FutureProofHomes/Satellite1-Enclosures/DIY Enclosures/In Ceiling Enclosures/pictures/Screws.png

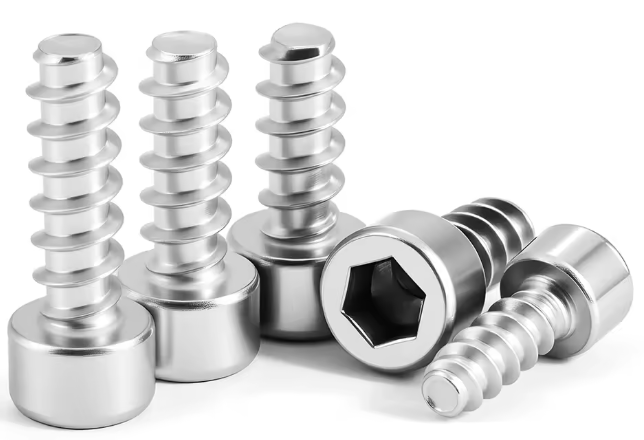
DIY Enclosures/In Ceiling Enclosures/pictures/Screws.png
