FutureProofHomes/Satellite1-Enclosures/OEM Enclosures/Satellite1 Smart Speaker Enclosure Kit/Geometry Files/STEP/Bonus/Minimalistic Chamber (optional 3525 speaker).step

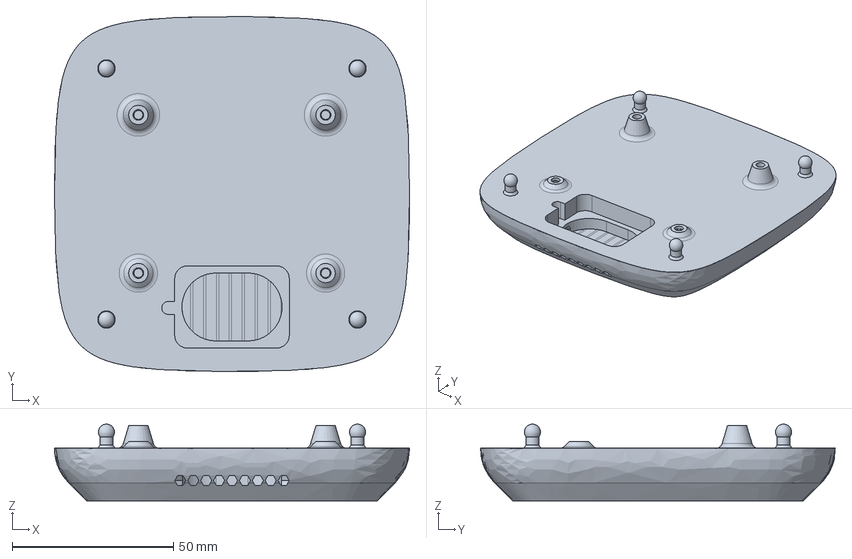
[picture p22: CAD file, 2026-02-08]
OEM Enclosures/Satellite1 Smart Speaker Enclosure Kit/Geometry Files/STEP/Bonus/Minimalistic Chamber (optional 3525 speaker).step
110.0 x 110.0 x 23.8 mm
