FutureProofHomes/Satellite1-Enclosures/OEM Enclosures/Satellite1 Smart Speaker Enclosure Kit/Geometry Files/STEP/LED Diffuser.step

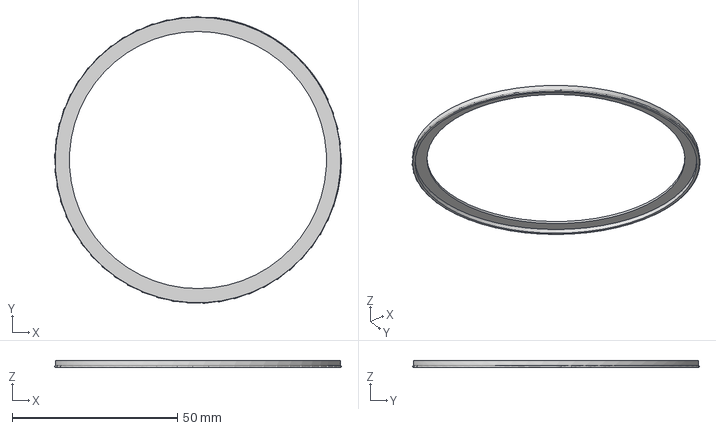
[picture p23: CAD file, 2025-12-31]
OEM Enclosures/Satellite1 Smart Speaker Enclosure Kit/Geometry Files/STEP/LED Diffuser.step
86.8 x 86.8 x 2.00 mm
