FutureProofHomes/Satellite1-Enclosures/OEM Enclosures/Satellite1 Smart Speaker Enclosure Kit/Geometry Files/STEP/MultiMaterial/Top Plate (MultiMaterial including diffuser).step

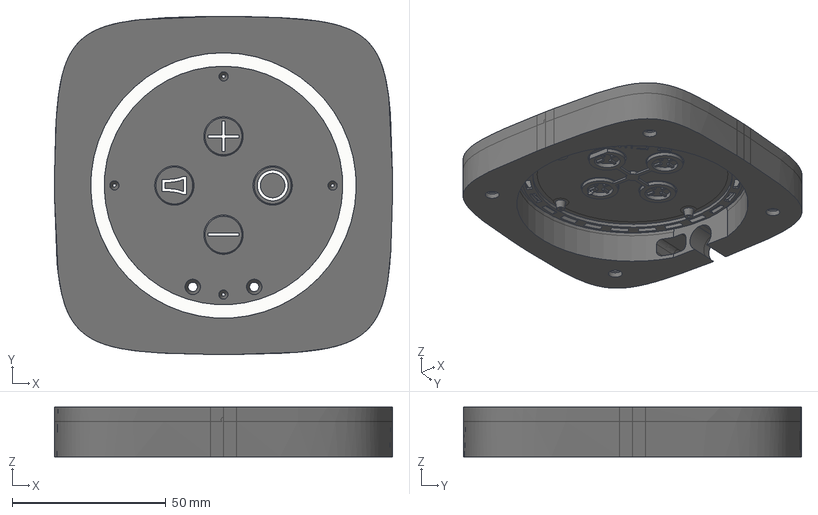
[picture p24: CAD file, 2025-12-31]
OEM Enclosures/Satellite1 Smart Speaker Enclosure Kit/Geometry Files/STEP/MultiMaterial/Top Plate (MultiMaterial including diffuser).step
110.0 x 110.0 x 16.2 mm
Top multimaterial
Speaker symbol led pipe (2)
Speaker symbol (1)
Minus symbol (1)
Ring symbol (1)
Plus symbol (1)
LED Ring diffuser
