FutureProofHomes/Satellite1-Enclosures/OEM Enclosures/Satellite1.1 Smart Speaker Enclosure Kit/Geometry Files/STL/Sat1.x large - Chamber back - Wifi pocket + Bass port.stl

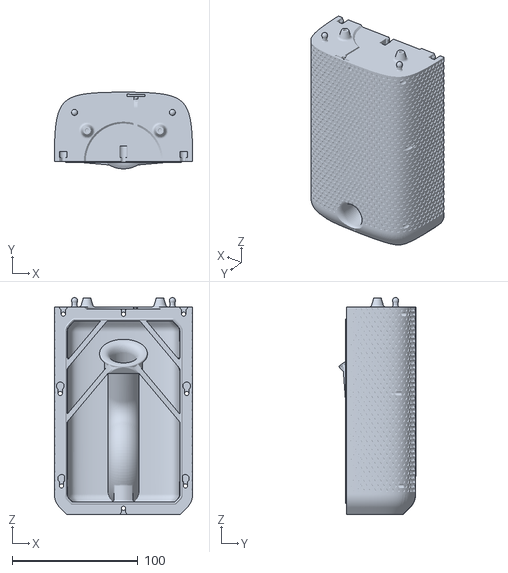
[picture p25: CAD file, 2026-07-22]
OEM Enclosures/Satellite1.1 Smart Speaker Enclosure Kit/Geometry Files/STL/Sat1.x large - Chamber back - Wifi pocket + Bass port.stl
110.0 x 61.0 x 172.5
