FutureProofHomes/Satellite1-Enclosures/OEM Enclosures/Satellite1.1 Smart Speaker Enclosure Kit/Sat 1.x Enclosure - singlematerial (Orca Slicer Projectfile).3mf

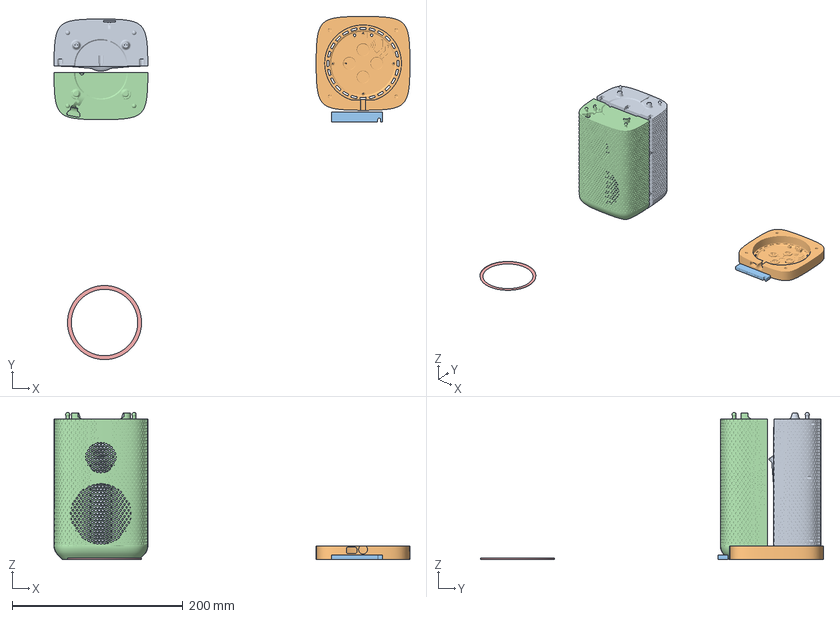
[picture p26: CAD file, 2026-04-05]
OEM Enclosures/Satellite1.1 Smart Speaker Enclosure Kit/Sat 1.x Enclosure - singlematerial (Orca Slicer Projectfile).3mf
417.2 x 402.1 x 172.5 mm
Sat1.x - Chamber back - Wifi pocket + Bass port.stl
Sat1.x - Top Plate single material.stl
Sat1.x - Screwing guide.stl
Sat1.x - Chamber front - FPH Woofer +Tweeter + LD2450 pocket.stl
Sat1.x - Top Plate single material - LED Diffuser.stl
