FutureProofHomes/Satellite1-Enclosures/DIY Enclosures/Cylindrical Enclosures/Bambu Studio - Sat1 Dev Kit Speaker Enclosure.3mf

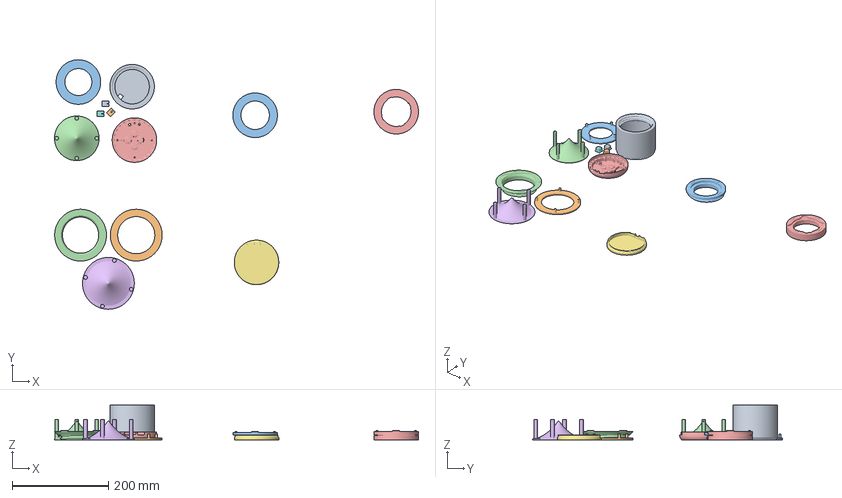
[picture p27: CAD file, 2025-05-12]
DIY Enclosures/Cylindrical Enclosures/Bambu Studio - Sat1 Dev Kit Speaker Enclosure.3mf
755.2 x 517.7 x 72.1 mm
Speaker Chamber Threaded.stl
Stand Lock Ring - GRS-3FR-4.stl
Speaker Adapter - RS75-4.stl
Speaker Adapter - GRS-3FR-4.stl
Speaker Adapter - TEBM46C-20N.stl
Speaker Stand - GRS 3FR-4.stl
(Optional) Dev Kit UFO Base for No Speaker.stl
1.5mm Wire Cover.stl
1mm Wire Cover.stl
2mm Wire Cover.stl
Lock Ring.stl
Speaker Stand.stl
Dev Kit UFO Enclosure.stl
