FutureProofHomes/Satellite1-Enclosures/DIY Enclosures/Cylindrical Enclosures/Geometry Files/STEP/General Parts/Speaker Chamber Threaded.step

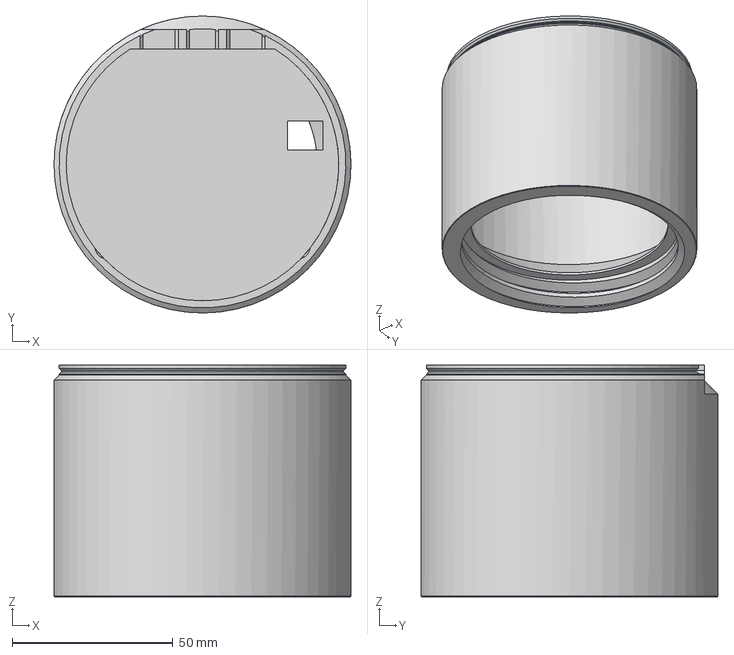
[picture p28: CAD file, 2025-05-12]
DIY Enclosures/Cylindrical Enclosures/Geometry Files/STEP/General Parts/Speaker Chamber Threaded.step
92.4 x 92.4 x 72.1 mm
