FutureProofHomes/Satellite1-Enclosures/DIY Enclosures/Squircle Enclosures/Geometry Files/STEP/Mid-Plate/Mid-Plate.step

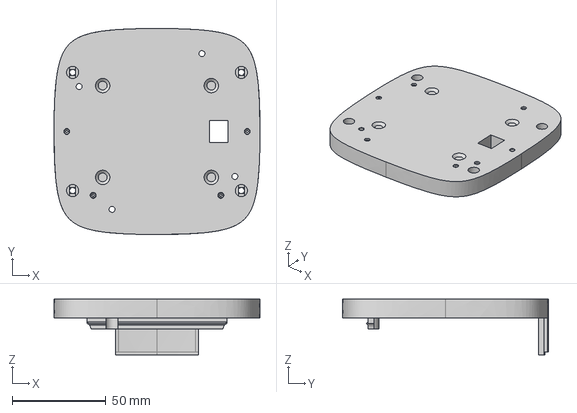
[picture p29: CAD file, 2025-06-02]
DIY Enclosures/Squircle Enclosures/Geometry Files/STEP/Mid-Plate/Mid-Plate.step
110.0 x 110.0 x 29.7 mm
