FutureProofHomes/Satellite1-Enclosures/DIY Enclosures/Squircle Enclosures/Geometry Files/STEP/Speaker Chamber/3-Watt Speaker Chamber.step

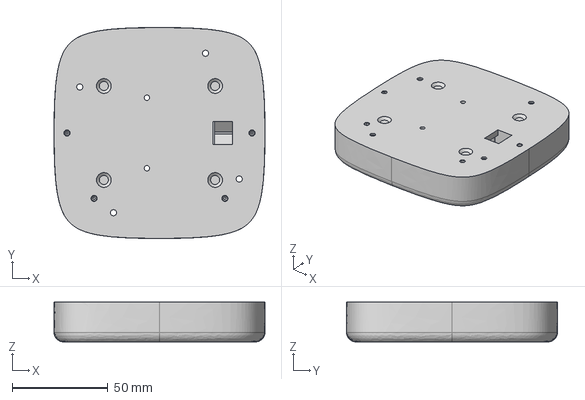
[picture p30: CAD file, 2025-06-04]
DIY Enclosures/Squircle Enclosures/Geometry Files/STEP/Speaker Chamber/3-Watt Speaker Chamber.step
110.0 x 110.0 x 20.7 mm
