FutureProofHomes/Satellite1-Enclosures/DIY Enclosures/Squircle Enclosures/Geometry Files/STEP/Squircle Top/Top Plate Snap-In Diffuser Ring.step

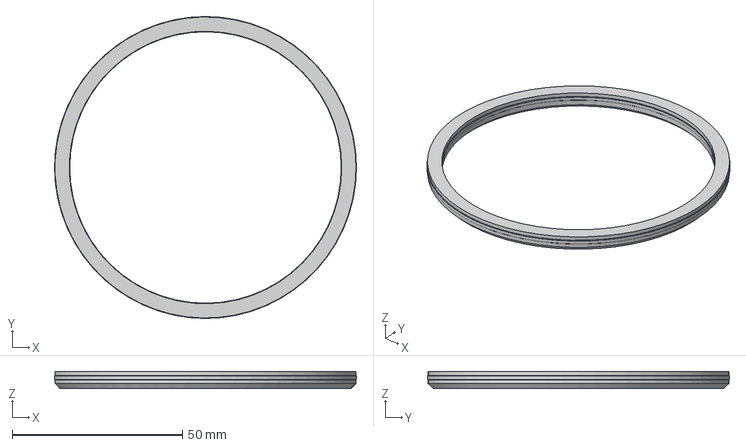
[picture p31: CAD file, 2025-06-11]
DIY Enclosures/Squircle Enclosures/Geometry Files/STEP/Squircle Top/Top Plate Snap-In Diffuser Ring.step
88.8 x 88.8 x 5.00 mm
