FutureProofHomes/Satellite1-Enclosures/DIY Enclosures/Squircle Enclosures/Geometry Files/STEP/Wire Covers/Wire Cover 1.5mm.step

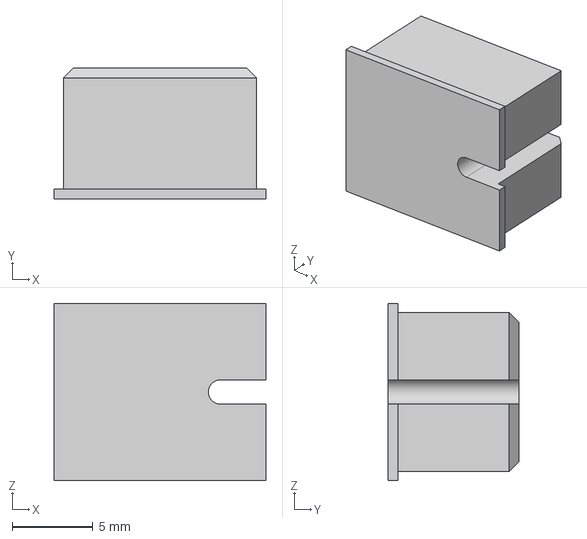
[picture p32: CAD file, 2025-06-03]
DIY Enclosures/Squircle Enclosures/Geometry Files/STEP/Wire Covers/Wire Cover 1.5mm.step
13.2 x 8.10 x 11.0 mm
