FutureProofHomes/Satellite1-Enclosures/OEM Enclosures/Satellite1 Smart Speaker Enclosure Kit/Geometry Files/STEP/Top Plate.step

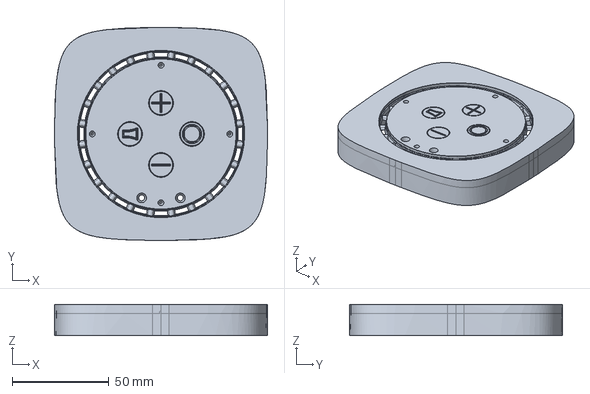
[picture p33: CAD file, 2025-12-31]
OEM Enclosures/Satellite1 Smart Speaker Enclosure Kit/Geometry Files/STEP/Top Plate.step
110.0 x 110.0 x 16.2 mm
