FutureProofHomes/Satellite1-Enclosures/OEM Enclosures/Satellite1.1 Smart Speaker Enclosure Kit/Geometry Files/STL/Sat1.x - Top Plate multi material.3mf

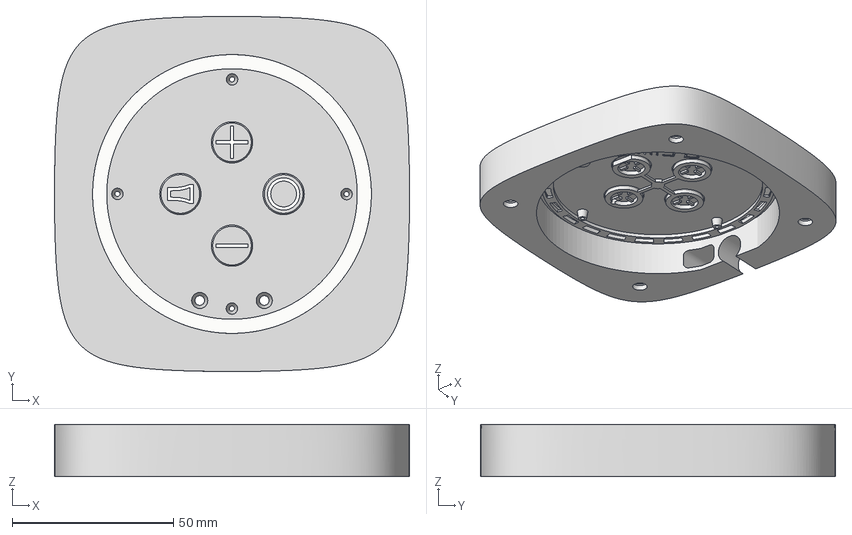
[picture p34: CAD file, 2026-04-05]
OEM Enclosures/Satellite1.1 Smart Speaker Enclosure Kit/Geometry Files/STL/Sat1.x - Top Plate multi material.3mf
110.0 x 110.0 x 16.1 mm
Diffuser
Minus symbol
Plus symbol
Ring symbol
Speaker symbol
Top multimaterial
