FutureProofHomes/Satellite1-Enclosures/OEM Enclosures/Satellite1.1 Smart Speaker Enclosure Kit/Sat 1.x Enclosure - multimaterial white (Bambu Studio Projectfile).3mf

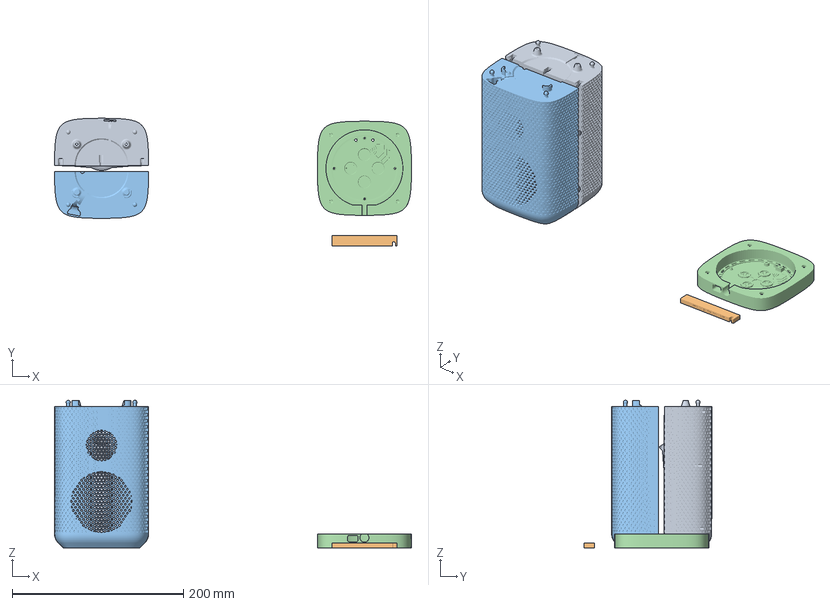
[picture p35: CAD file, 2026-04-05]
OEM Enclosures/Satellite1.1 Smart Speaker Enclosure Kit/Sat 1.x Enclosure - multimaterial white (Bambu Studio Projectfile).3mf
417.2 x 149.0 x 172.5 mm
Chamber back - Wifi pocket + Bass port.stl
Screw guide
Chamber front - FPH Woofer +Tweeter + LD2450 pocket.stl
Top - Multimaterial
