FutureProofHomes/Satellite1-Enclosures/DIY Enclosures/Cylindrical Enclosures/Geometry Files/STEP/Speaker - GRS 3FR-4/Speaker Stand - GRS 3FR-4.step

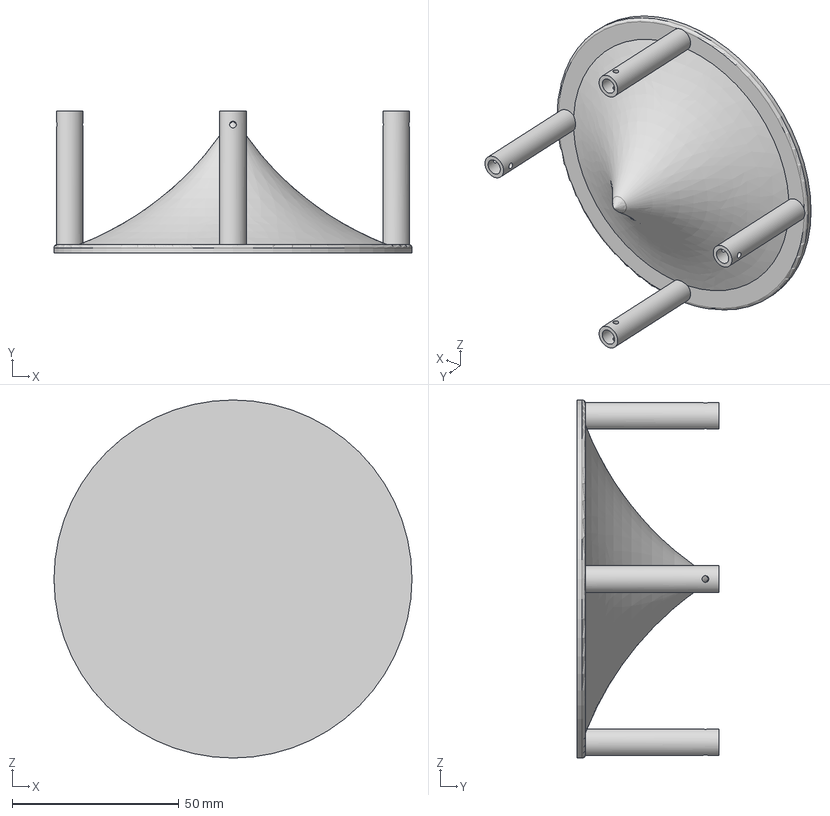
[picture p37: CAD file, 2025-05-03]
DIY Enclosures/Cylindrical Enclosures/Geometry Files/STEP/Speaker - GRS 3FR-4/Speaker Stand - GRS 3FR-4.step
107.5 x 42.5 x 107.5 mm
