FutureProofHomes/Satellite1-Enclosures/DIY Enclosures/Squircle Enclosures/Geometry Files/STEP/Speaker Chamber/3-Watt Speaker Chamber Legs x 4.step

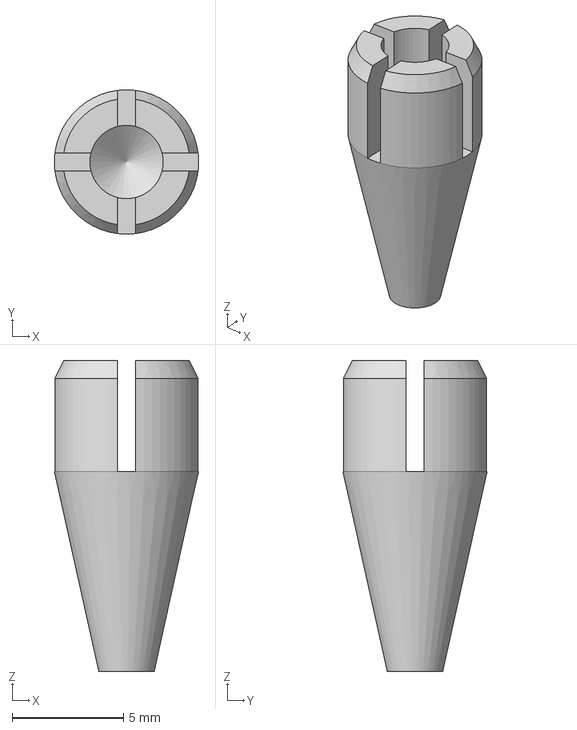
[picture p38: CAD file, 2025-06-04]
DIY Enclosures/Squircle Enclosures/Geometry Files/STEP/Speaker Chamber/3-Watt Speaker Chamber Legs x 4.step
6.50 x 6.49 x 14.0 mm
