FutureProofHomes/Satellite1-Enclosures/DIY Enclosures/Squircle Enclosures/Geometry Files/STEP/Speaker Plates/25-Watt Speaker Plate Tectonic TEBM46C20N-4 v5.step

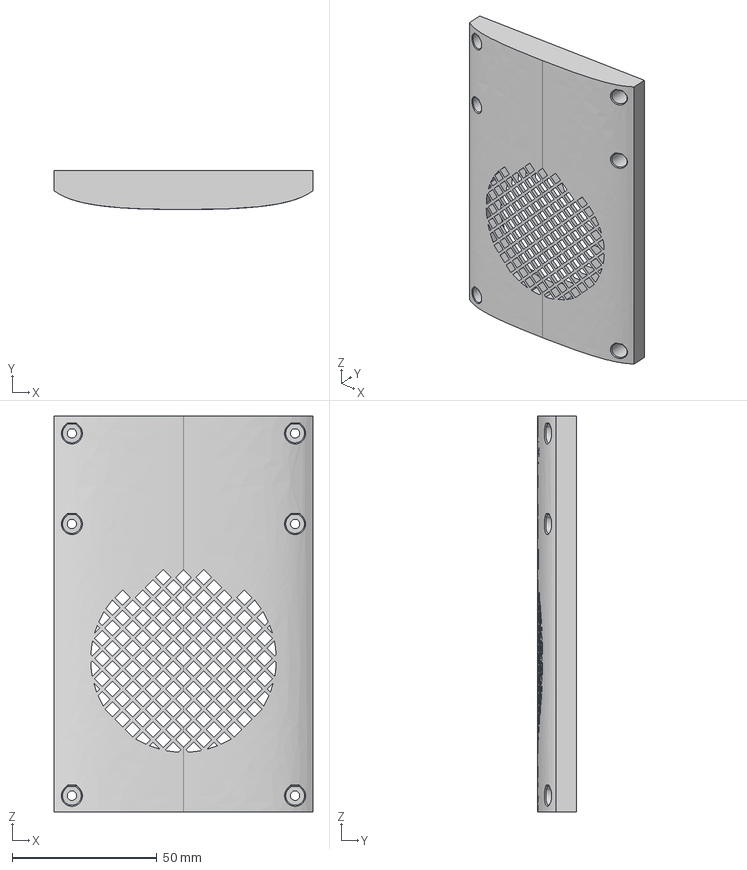
[picture p39: CAD file, 2025-05-26]
DIY Enclosures/Squircle Enclosures/Geometry Files/STEP/Speaker Plates/25-Watt Speaker Plate Tectonic TEBM46C20N-4 v5.step
89.2 x 13.5 x 136.6 mm
