FutureProofHomes/Satellite1-Enclosures/DIY Enclosures/Squircle Enclosures/Geometry Files/STEP/Squircle Top/Top Plate.step

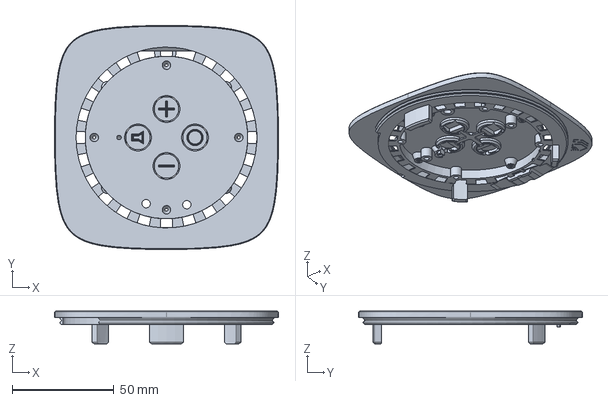
[picture p40: CAD file, 2025-06-11]
DIY Enclosures/Squircle Enclosures/Geometry Files/STEP/Squircle Top/Top Plate.step
110.0 x 110.0 x 16.0 mm
