FutureProofHomes/Satellite1-Enclosures/OEM Enclosures/Satellite1.1 Smart Speaker Enclosure Kit/Sat 1.x Enclosure - singlematerial (Bambu Studio Projectfile).3mf

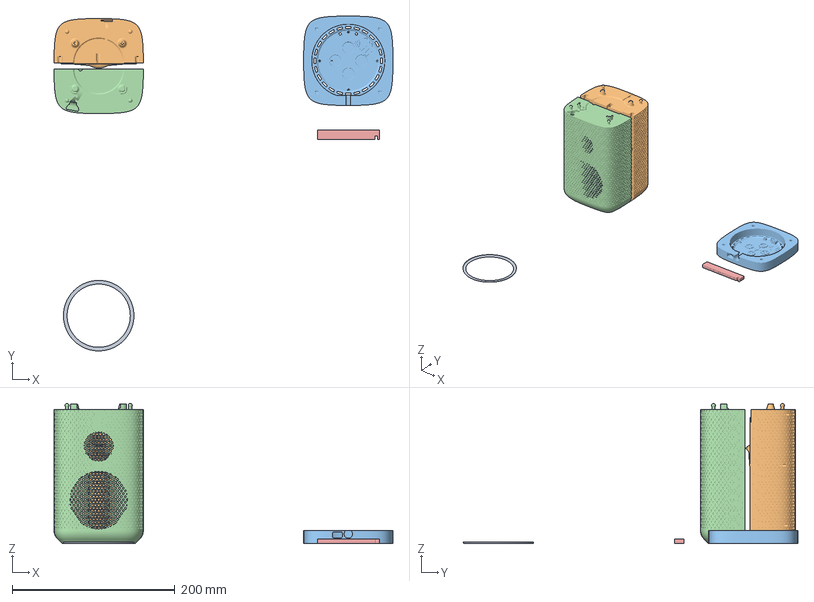
[picture p42: CAD file, 2026-04-05]
OEM Enclosures/Satellite1.1 Smart Speaker Enclosure Kit/Sat 1.x Enclosure - singlematerial (Bambu Studio Projectfile).3mf
417.2 x 412.1 x 172.5 mm
Top - LED diffuser.stl
Chamber back - Wifi pocket + Bass port.stl
Top.stl
Chamber front - FPH Woofer +Tweeter + LD2450 pocket.stl
Screw guide
