FutureProofHomes/Satellite1-Enclosures/DIY Enclosures/Cylindrical Enclosures/Geometry Files/STEP/General Parts/(Optional) Dev Kit UFO Base for No Speaker.step

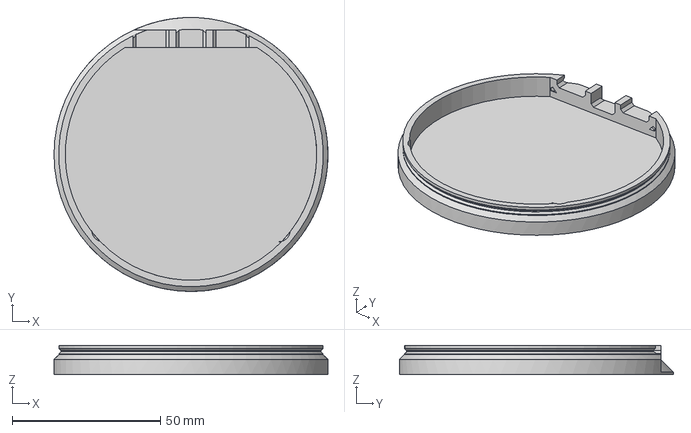
[picture p43: CAD file, 2025-05-06]
DIY Enclosures/Cylindrical Enclosures/Geometry Files/STEP/General Parts/(Optional) Dev Kit UFO Base for No Speaker.step
92.4 x 92.4 x 9.80 mm
