FutureProofHomes/Satellite1-Enclosures/DIY Enclosures/Squircle Enclosures/Geometry Files/STEP/Speaker Chamber/15-Watt Speaker Chamber.step

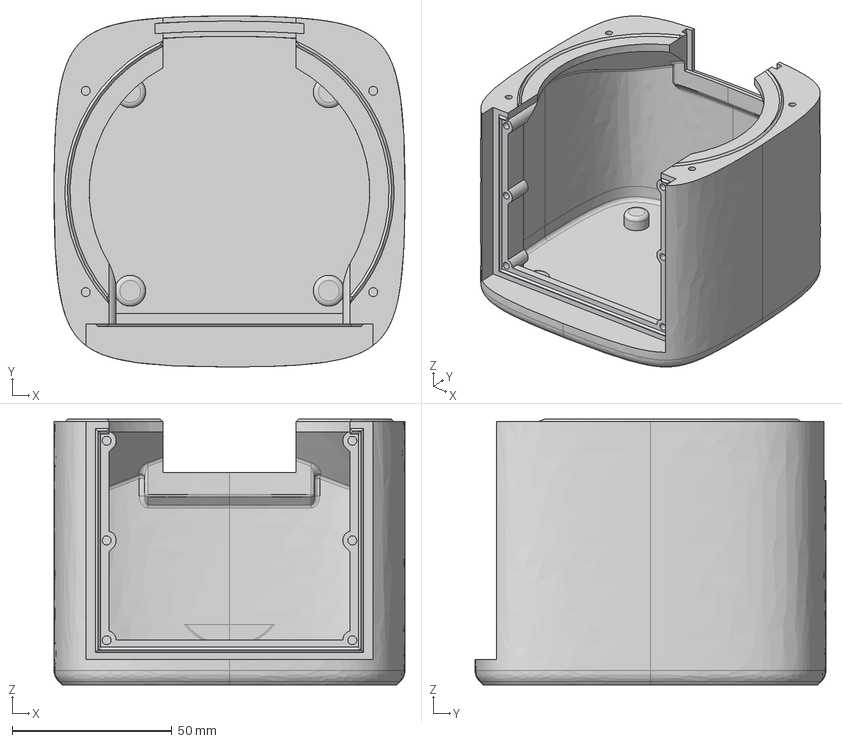
[picture p44: CAD file, 2025-06-04]
DIY Enclosures/Squircle Enclosures/Geometry Files/STEP/Speaker Chamber/15-Watt Speaker Chamber.step
110.0 x 110.0 x 83.3 mm
