FutureProofHomes/Satellite1-Enclosures/DIY Enclosures/Cylindrical Enclosures/Geometry Files/STEP/General Parts/1.5mm Wire Cover.step

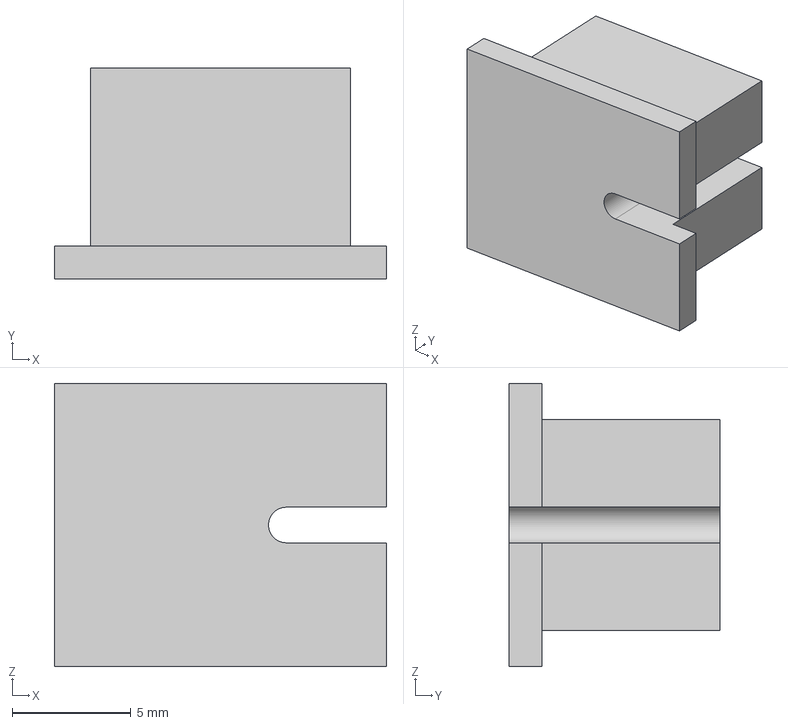
[picture p48: CAD file, 2025-05-06]
DIY Enclosures/Cylindrical Enclosures/Geometry Files/STEP/General Parts/1.5mm Wire Cover.step
14.0 x 8.90 x 11.9 mm
