FutureProofHomes/Satellite1-Enclosures/DIY Enclosures/Squircle Enclosures/Geometry Files/STEP/Speaker Chamber/25-Watt Speaker Chamber Anti-Slip Ring.step

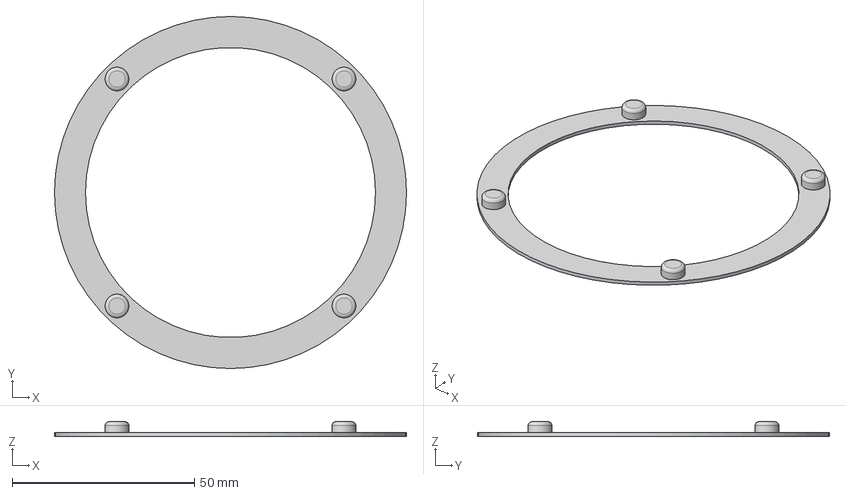
[picture p49: CAD file, 2025-05-26]
DIY Enclosures/Squircle Enclosures/Geometry Files/STEP/Speaker Chamber/25-Watt Speaker Chamber Anti-Slip Ring.step
96.5 x 96.5 x 4.00 mm
