FutureProofHomes/Satellite1-Enclosures/DIY Enclosures/Squircle Enclosures/Geometry Files/STEP/Speaker Plates/25-Watt Speaker Plate Dayton Audio PC83-4 3in.step

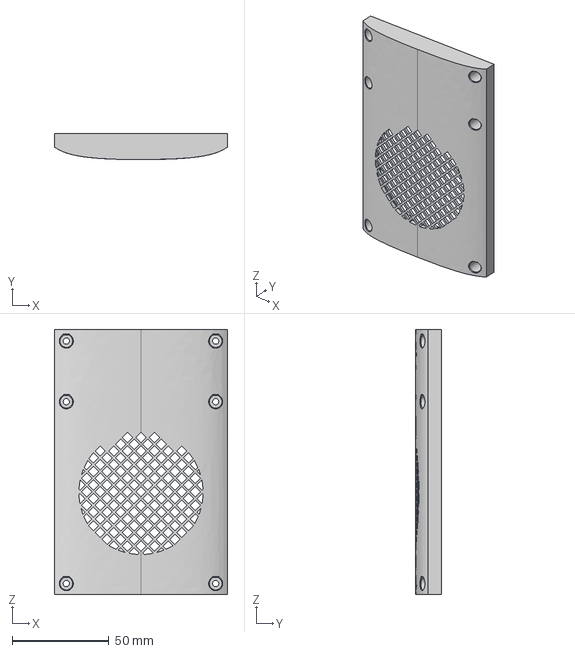
[picture p50: CAD file, 2025-05-26]
DIY Enclosures/Squircle Enclosures/Geometry Files/STEP/Speaker Plates/25-Watt Speaker Plate Dayton Audio PC83-4 3in.step
89.2 x 13.5 x 136.6 mm
