FutureProofHomes/Satellite1-Enclosures/DIY Enclosures/Squircle Enclosures/Geometry Files/STEP/Squircle Top/Top Plate MM Diffuser Ring.step

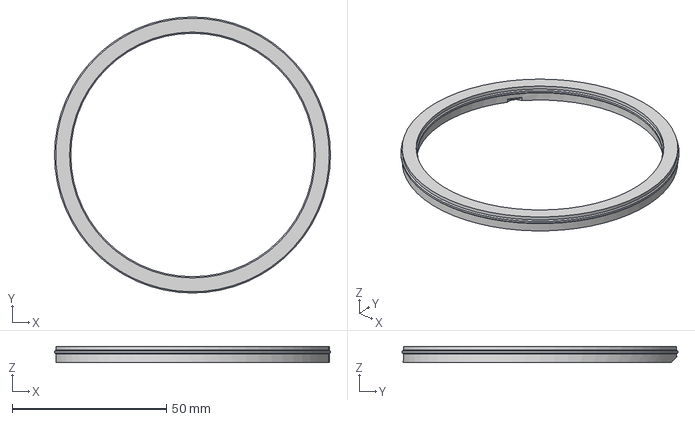
[picture p51: CAD file, 2025-06-11]
DIY Enclosures/Squircle Enclosures/Geometry Files/STEP/Squircle Top/Top Plate MM Diffuser Ring.step
89.6 x 89.6 x 5.20 mm
