FutureProofHomes/Satellite1-Enclosures/DIY Enclosures/Cylindrical Enclosures/Geometry Files/STEP/General Parts/Dev Kit UFO Enclosure.step

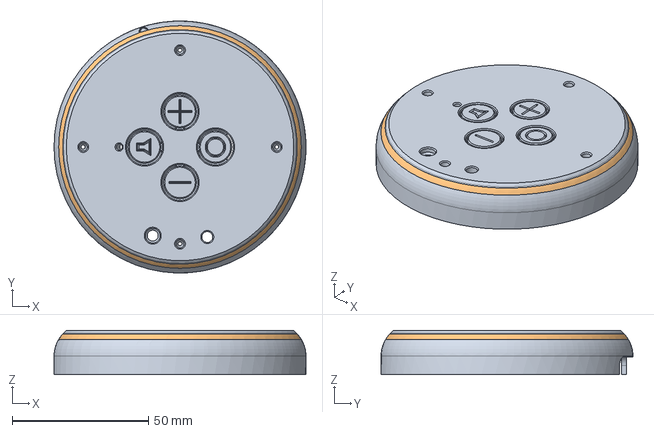
[picture p52: CAD file, 2025-05-06]
DIY Enclosures/Cylindrical Enclosures/Geometry Files/STEP/General Parts/Dev Kit UFO Enclosure.step
92.4 x 92.4 x 16.2 mm
