FutureProofHomes/Satellite1-Enclosures/DIY Enclosures/Squircle Enclosures/Geometry Files/STEP/Squircle Top/Top Plate MM Buttons.step

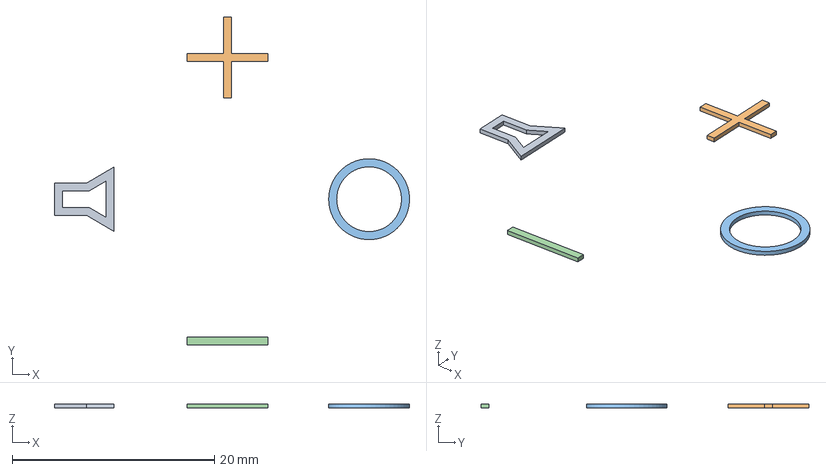
[picture p53: CAD file, 2025-06-04]
DIY Enclosures/Squircle Enclosures/Geometry Files/STEP/Squircle Top/Top Plate MM Buttons.step
35.1 x 32.4 x 0.4 mm
