FutureProofHomes/Satellite1-Enclosures/DIY Enclosures/Cylindrical Enclosures/Geometry Files/STEP/General Parts/Lock Ring.step

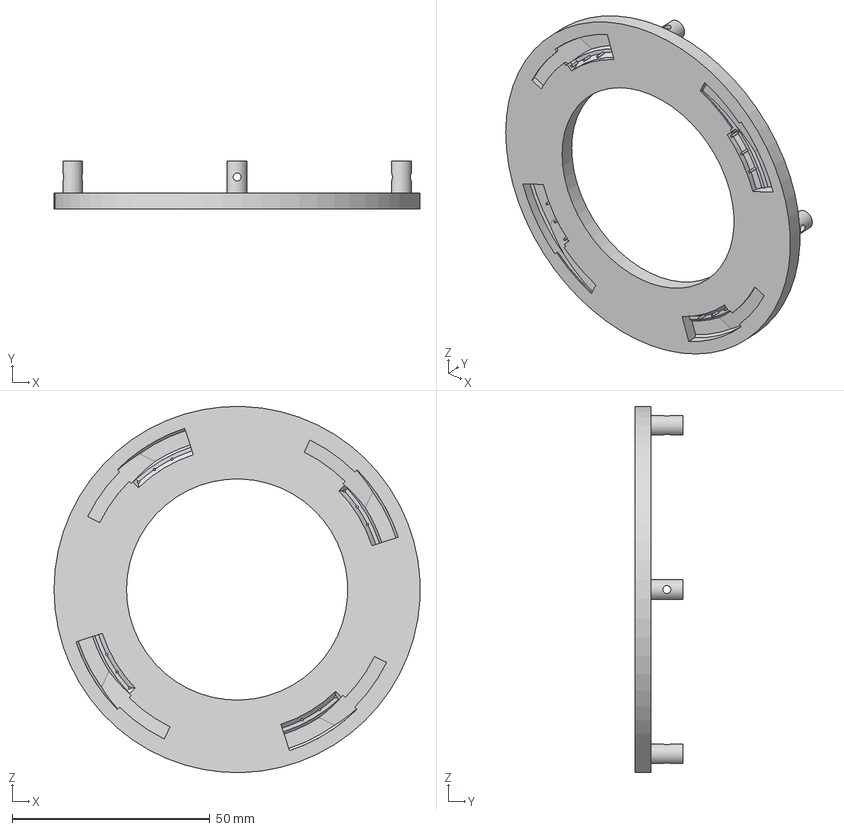
[picture p54: CAD file, 2025-05-06]
DIY Enclosures/Cylindrical Enclosures/Geometry Files/STEP/General Parts/Lock Ring.step
92.4 x 12.0 x 92.5 mm
