FutureProofHomes/Satellite1-Enclosures/DIY Enclosures/Squircle Enclosures/Geometry Files/STEP/Squircle Top/PCB Spacer.step

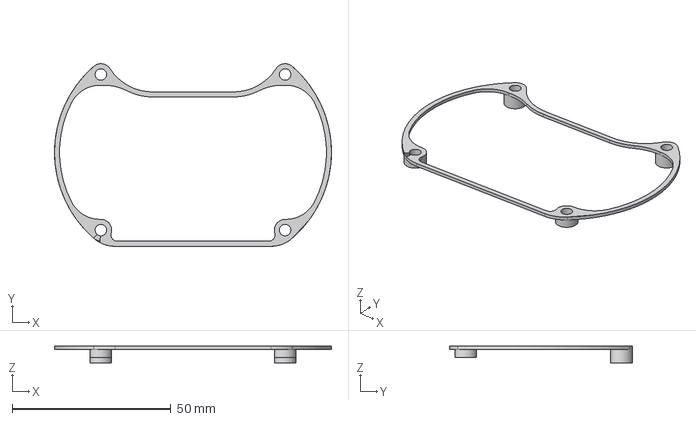
[picture p55: CAD file, 2025-05-26]
DIY Enclosures/Squircle Enclosures/Geometry Files/STEP/Squircle Top/PCB Spacer.step
87.2 x 57.5 x 5.20 mm
