FutureProofHomes/Satellite1-Enclosures/DIY Enclosures/In Ceiling Enclosures/pictures/In Ceiling Mini assembled backview.jpg

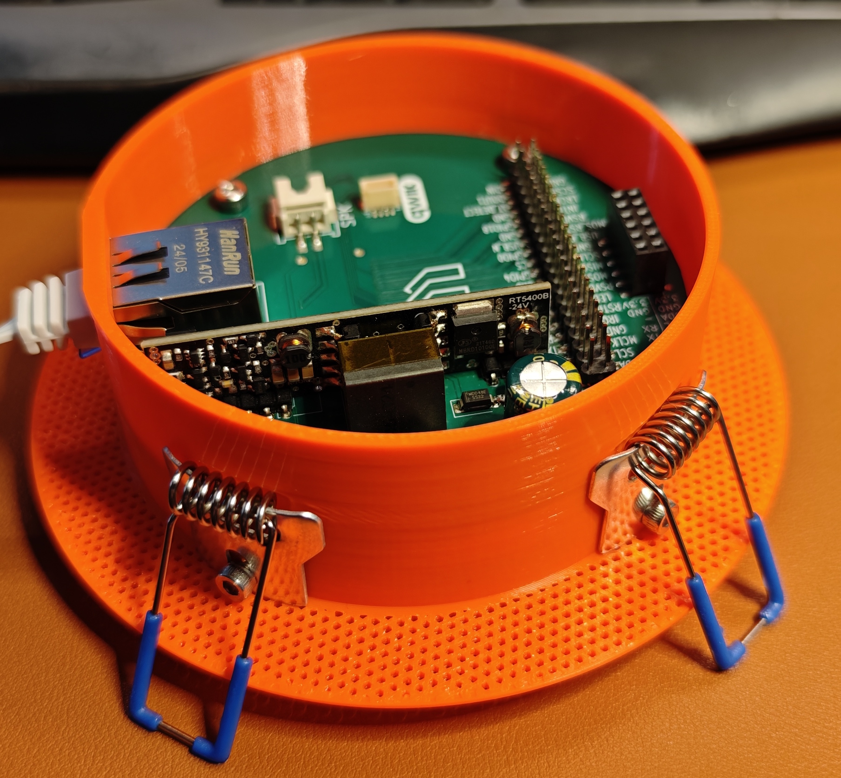
DIY Enclosures/In Ceiling Enclosures/pictures/In Ceiling Mini assembled backview.jpg
